vagovszky/iot/images/board/board_bottom.png

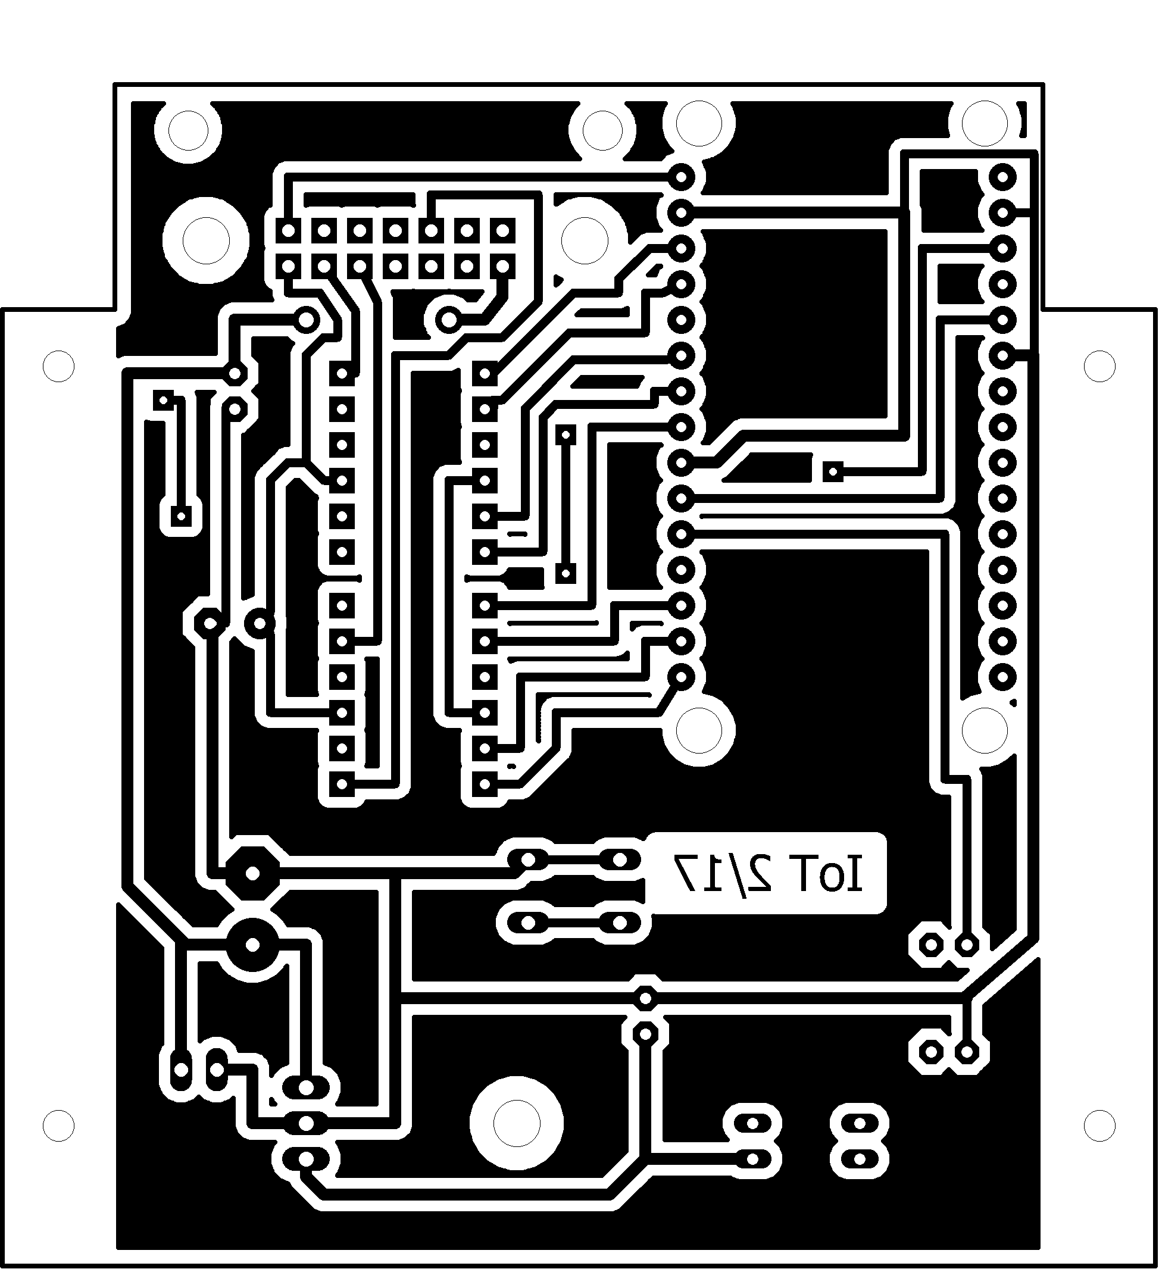
images/board/board_bottom.png
