vagovszky/iot/images/board/board_top.png

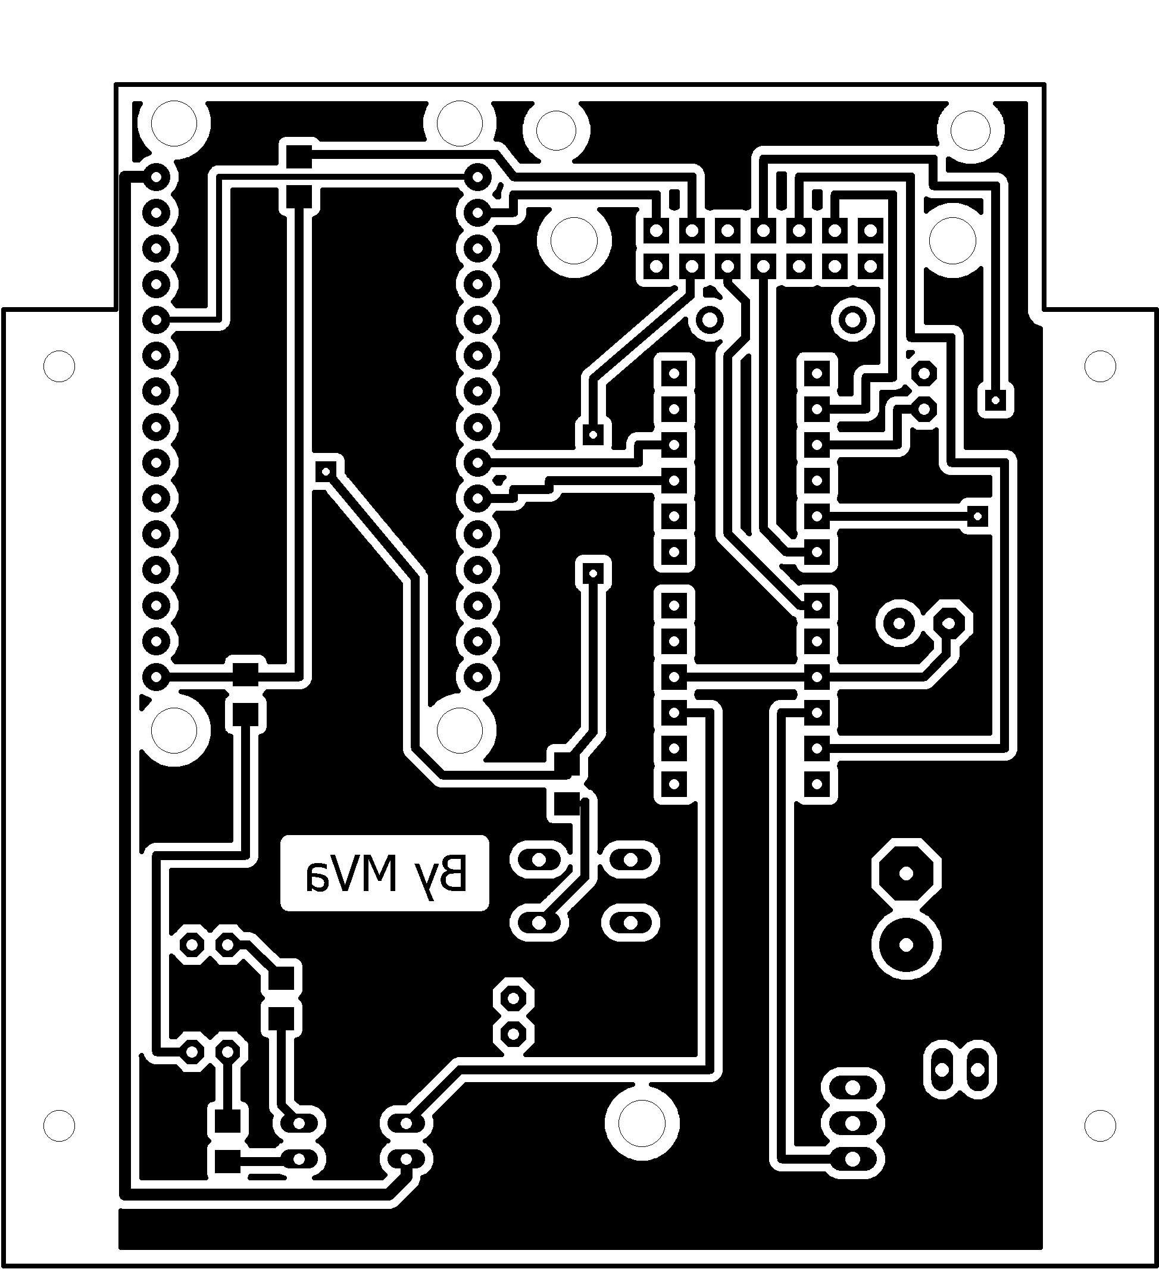
images/board/board_top.png
