vagovszky/iot/images/board/mod_io_board_bottom.png

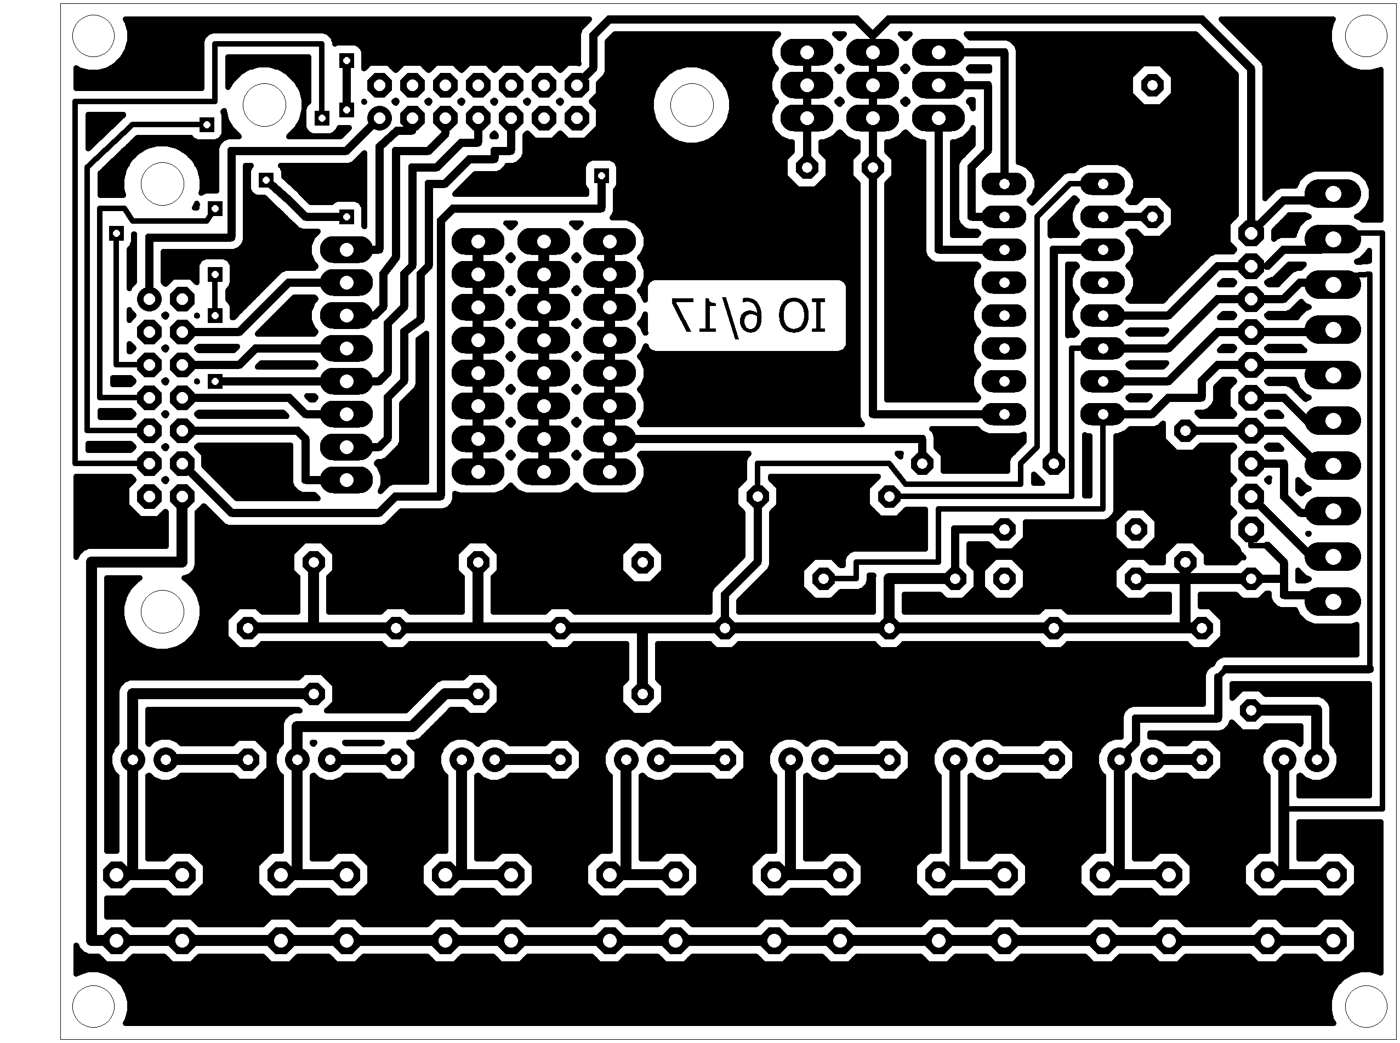
images/board/mod_io_board_bottom.png
