vagovszky/iot/images/board/mod_io_board_bottom_mask.png

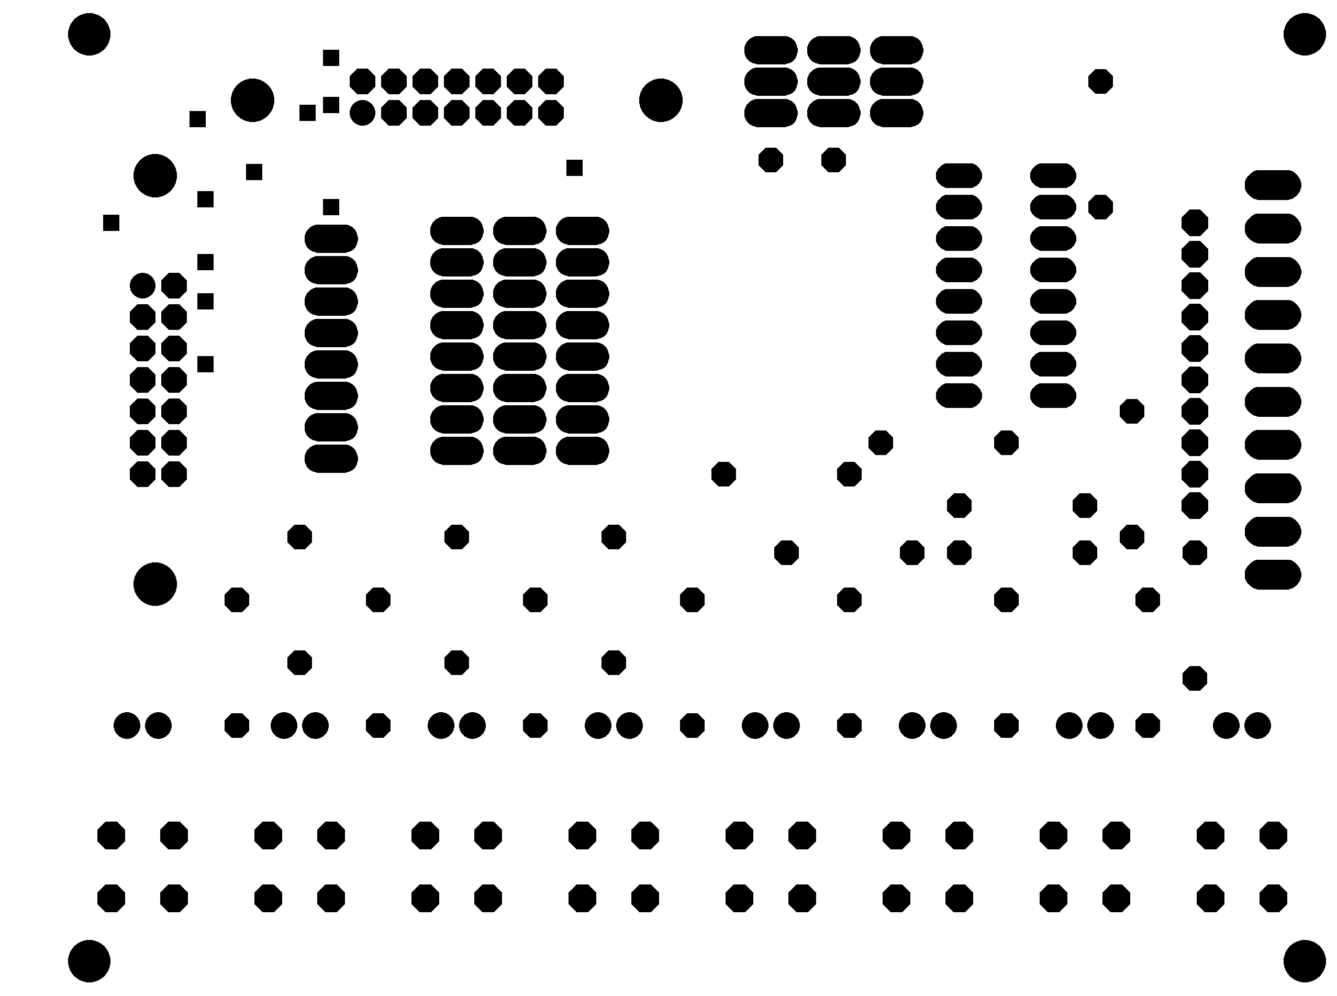
images/board/mod_io_board_bottom_mask.png
