vagovszky/iot/images/board/mod_io_board_top.png

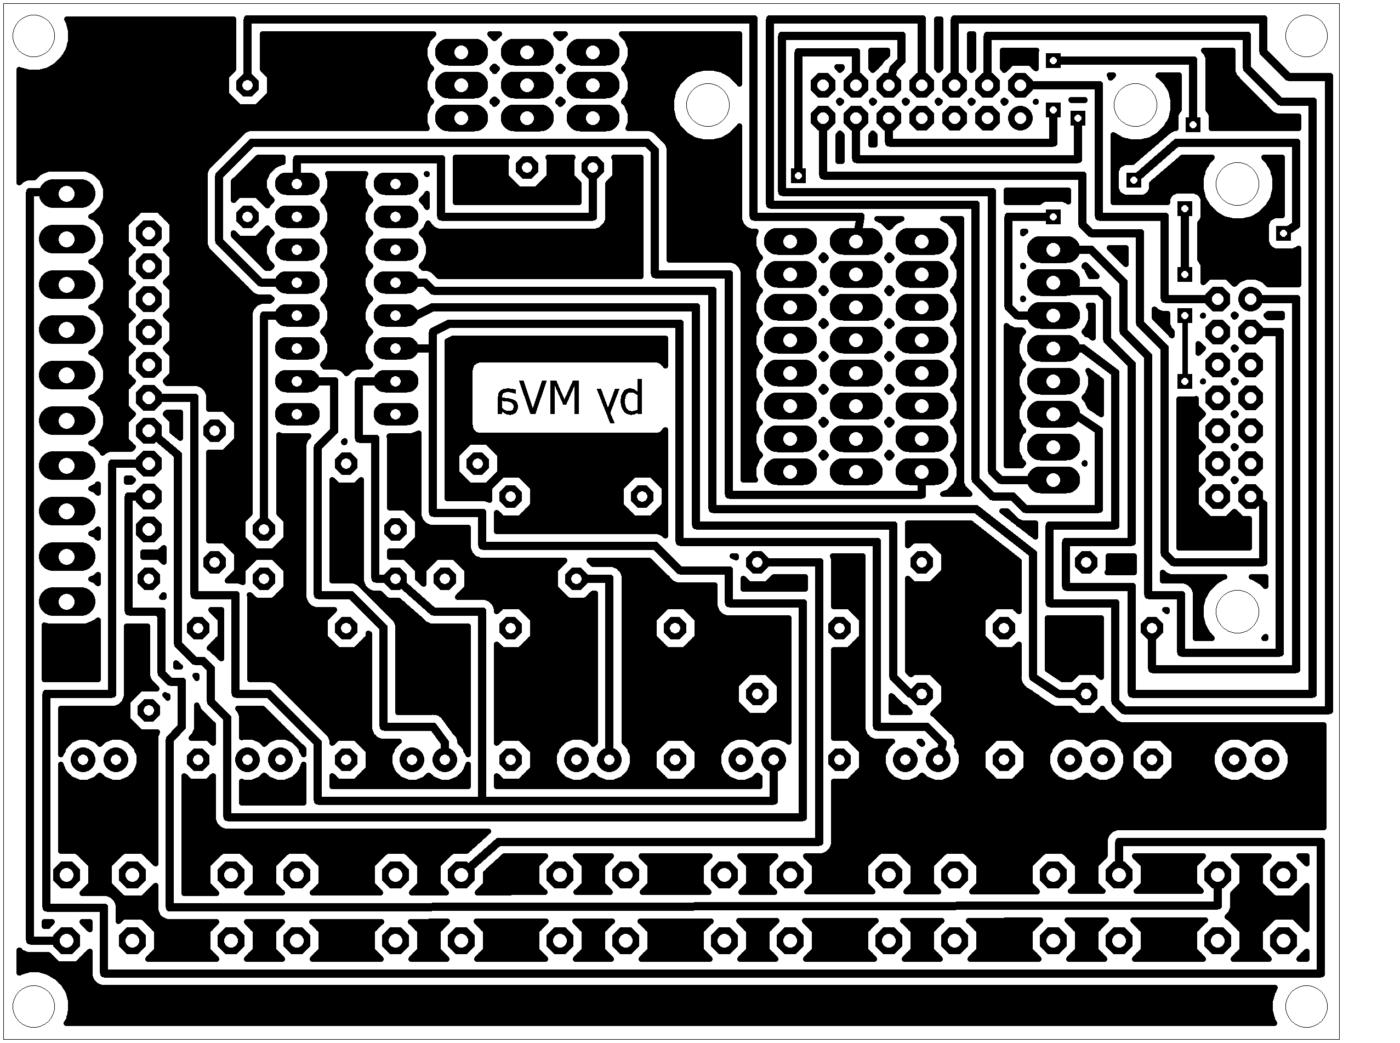
images/board/mod_io_board_top.png
