vagovszky/iot/images/board/mod_io_board_top_mask.png

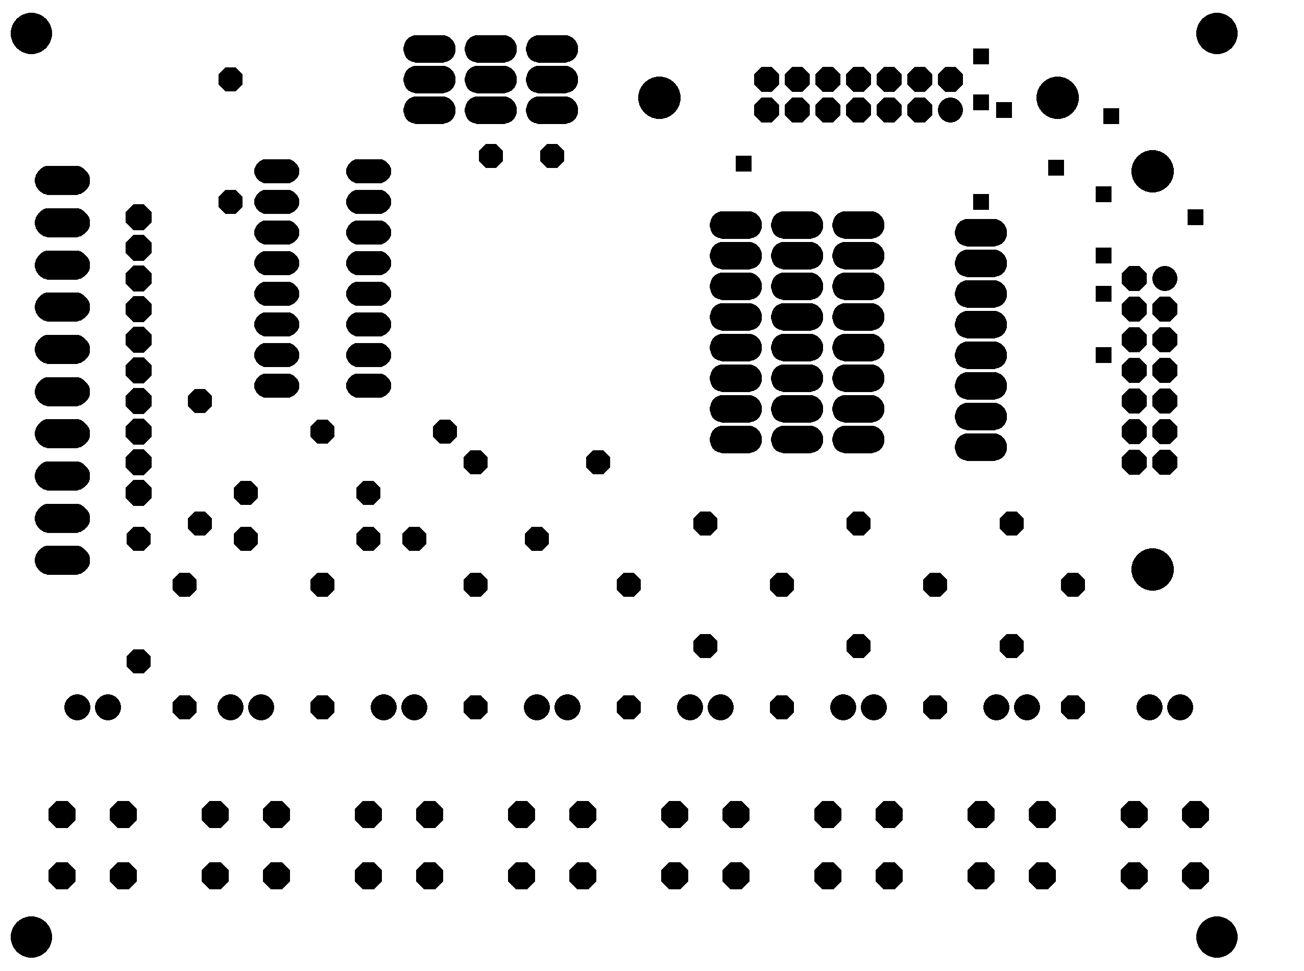
images/board/mod_io_board_top_mask.png
