vagovszky/iot/images/board/mod_temp_board_600dpi.png

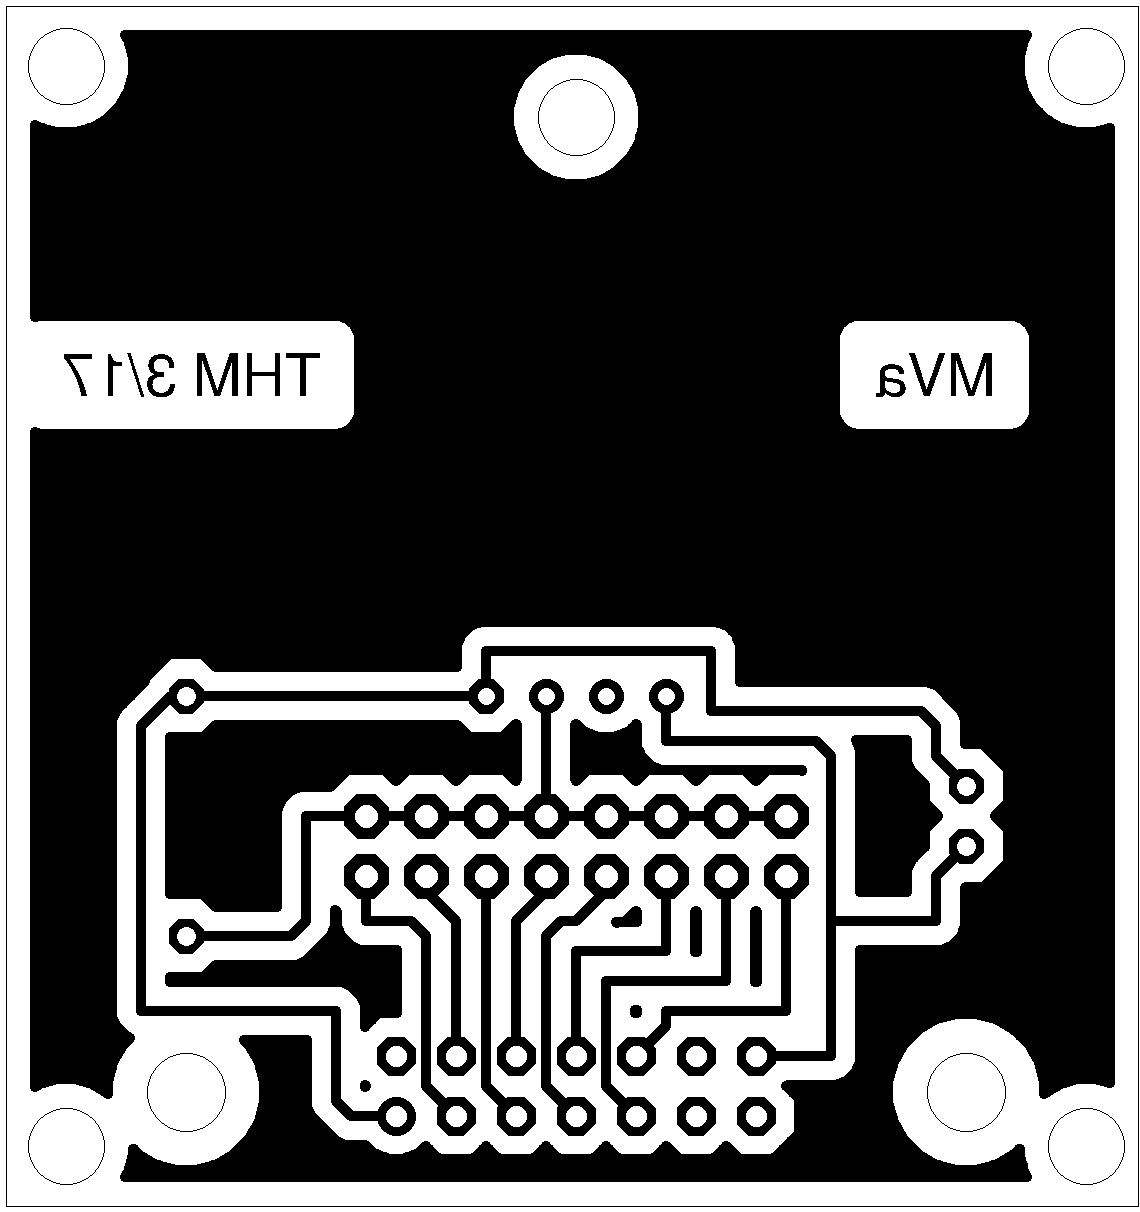
images/board/mod_temp_board_600dpi.png
