vagovszky/iot/images/board/mod_temp_mask_600dpi.png

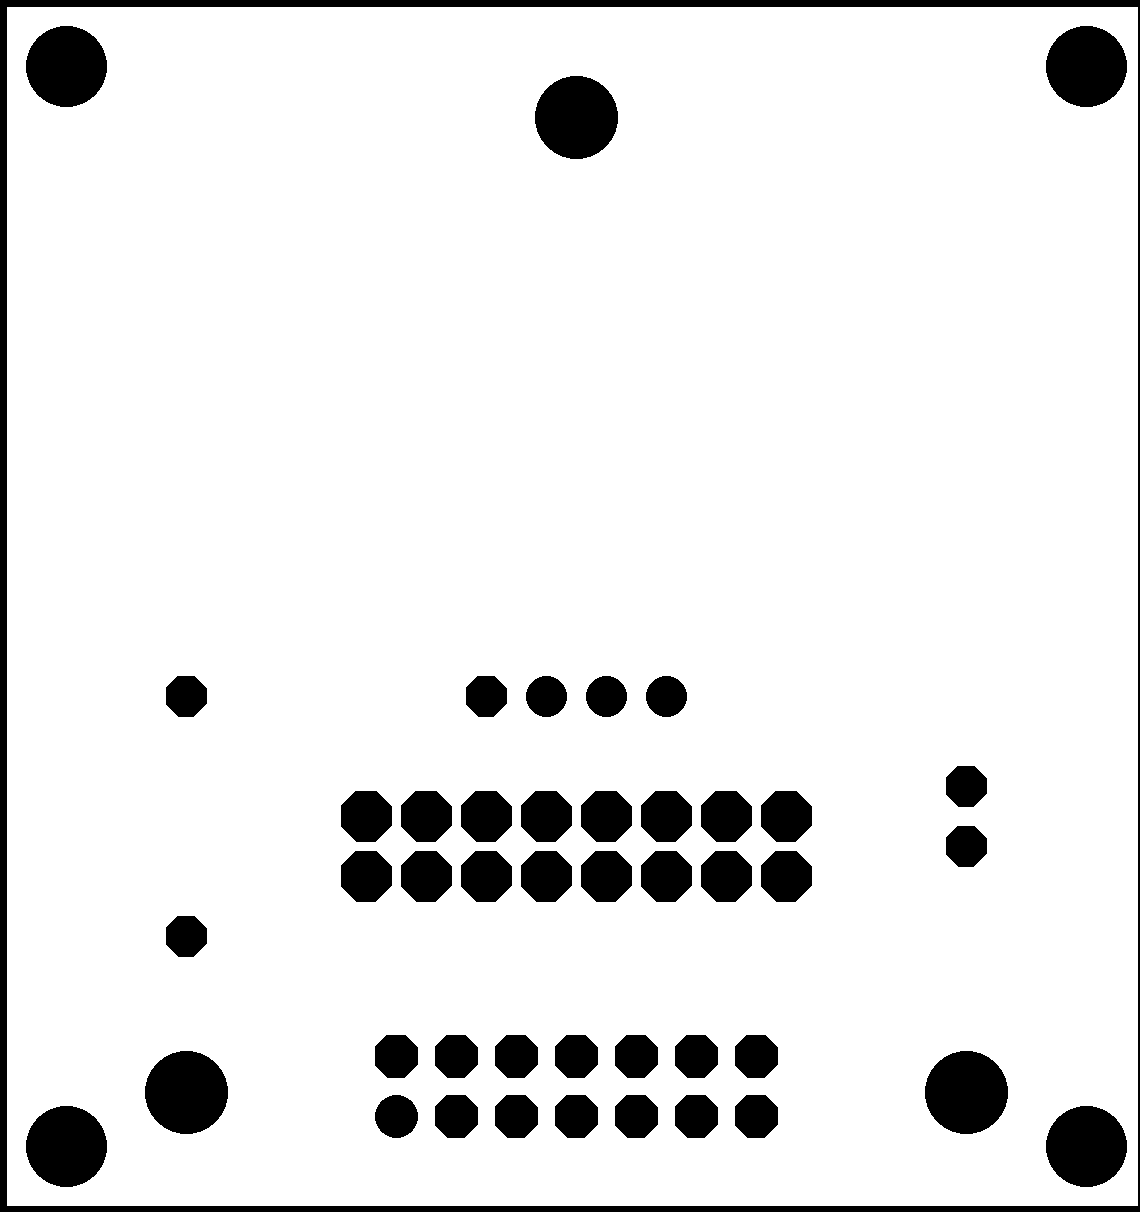
images/board/mod_temp_mask_600dpi.png
