vagovszky/iot/images/board/osaz.png

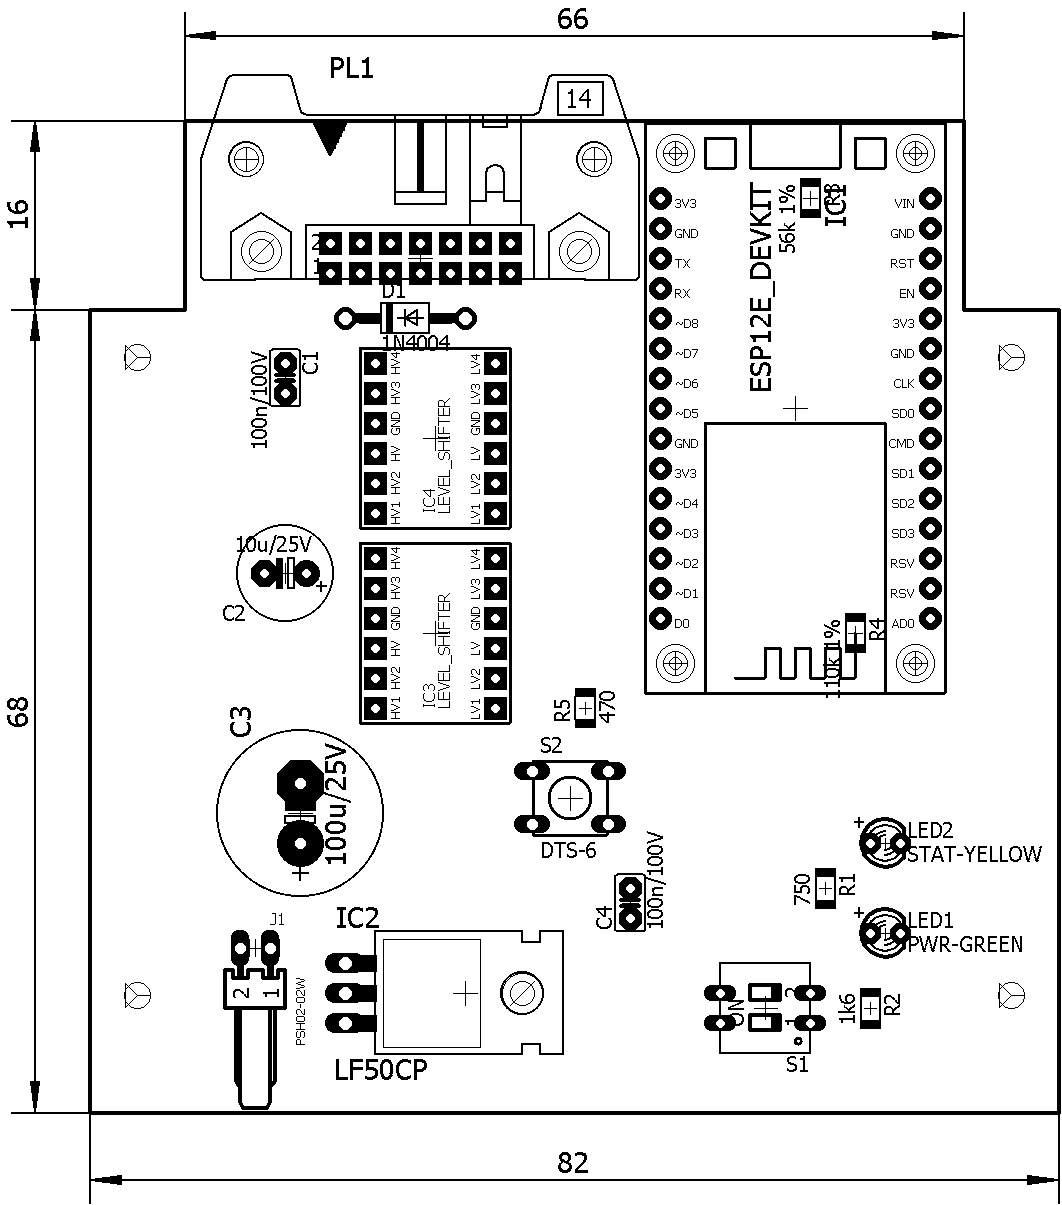
images/board/osaz.png
