vagovszky/iot/images/fotky/deska-osazena.jpg

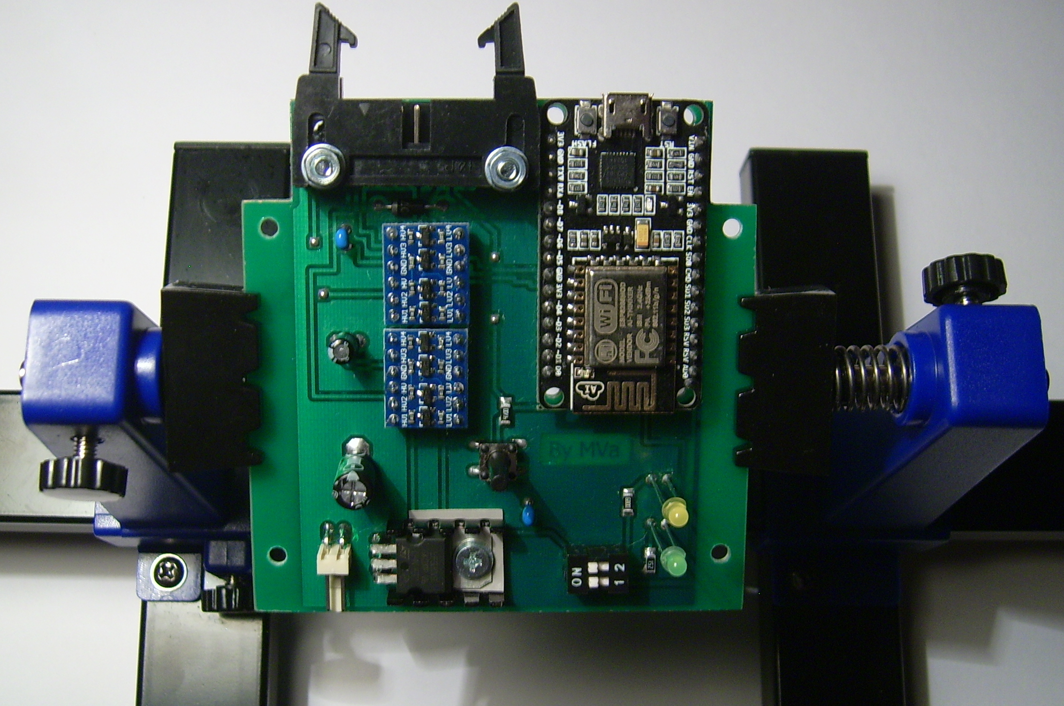
images/fotky/deska-osazena.jpg
