vagovszky/iot/images/fotky/deska-pred-vrtanim.jpg

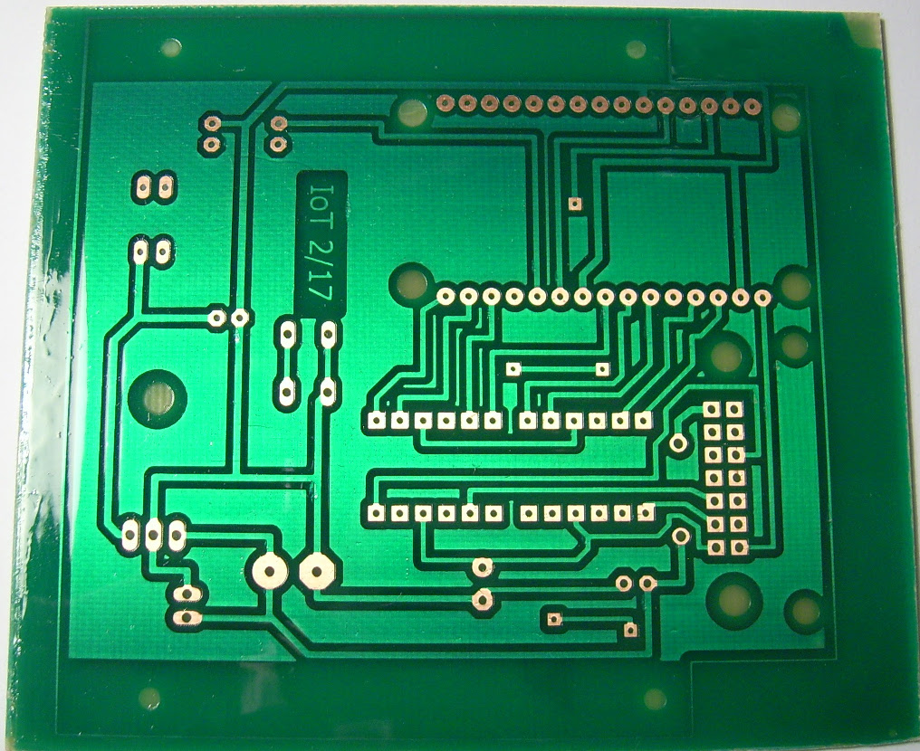
images/fotky/deska-pred-vrtanim.jpg
