vagovszky/iot/images/fotky/modul-hlavni.jpg

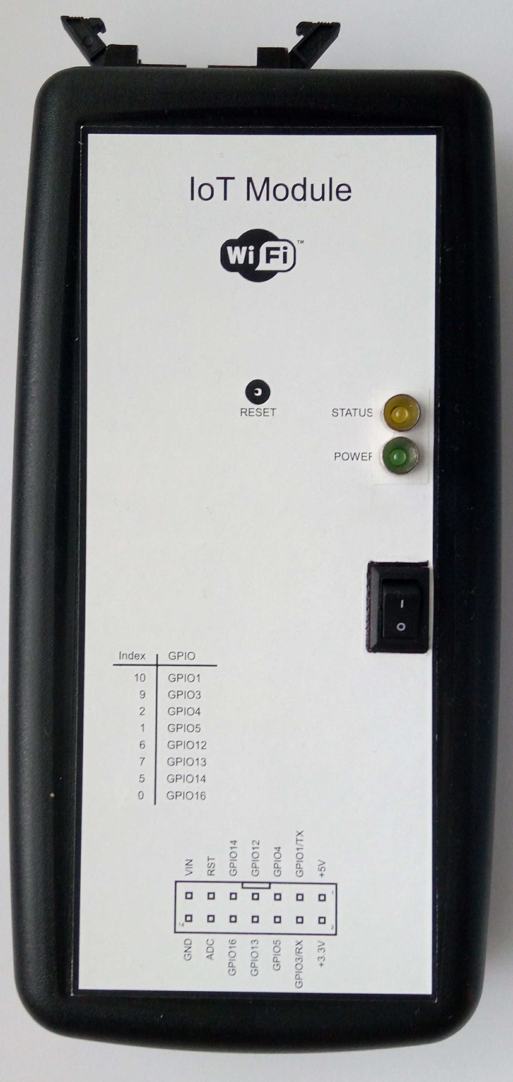
images/fotky/modul-hlavni.jpg
