vagovszky/iot/images/fotky/modul-io.jpg

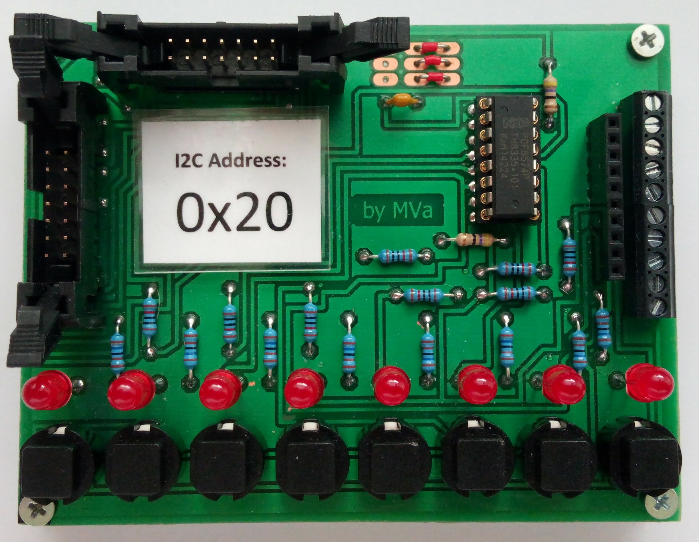
images/fotky/modul-io.jpg
