vagovszky/iot/images/fotky/modul-otevreny.jpg

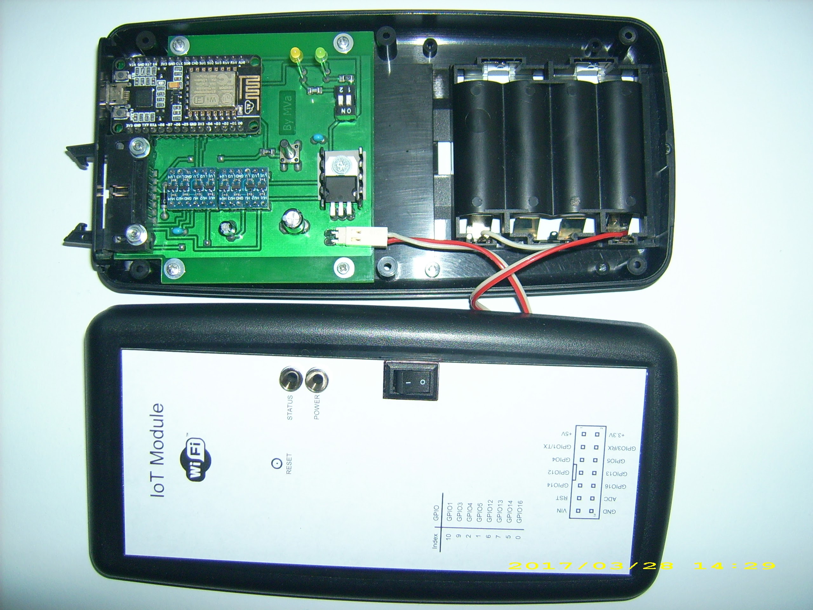
images/fotky/modul-otevreny.jpg
