vagovszky/iot/images/fotky/modul-teplota-vlhkost.jpg

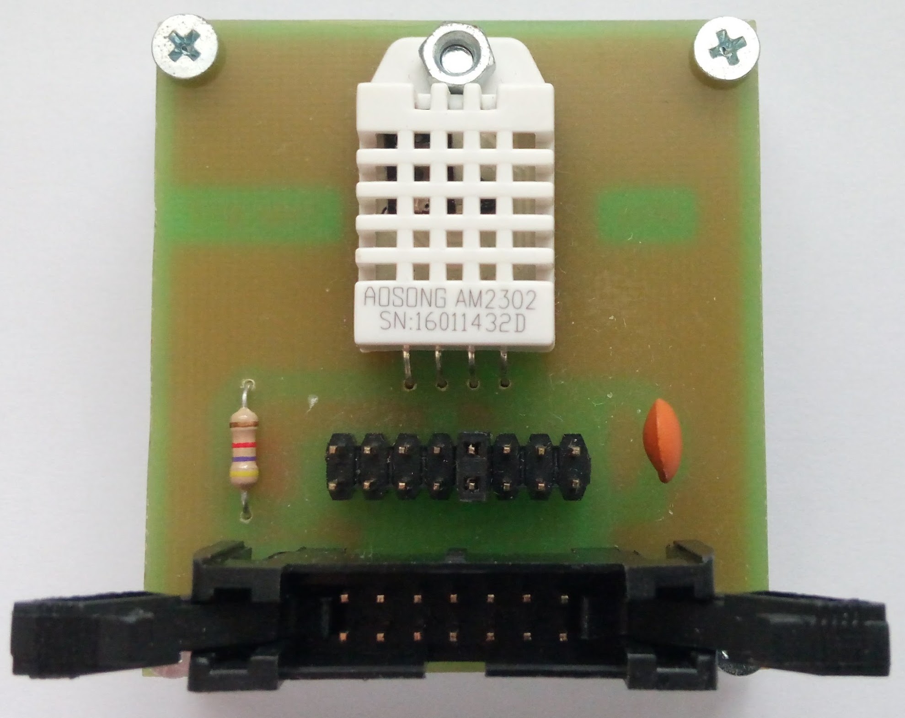
images/fotky/modul-teplota-vlhkost.jpg
