vagovszky/iot/images/fotky/modul-zadni-strana.jpg

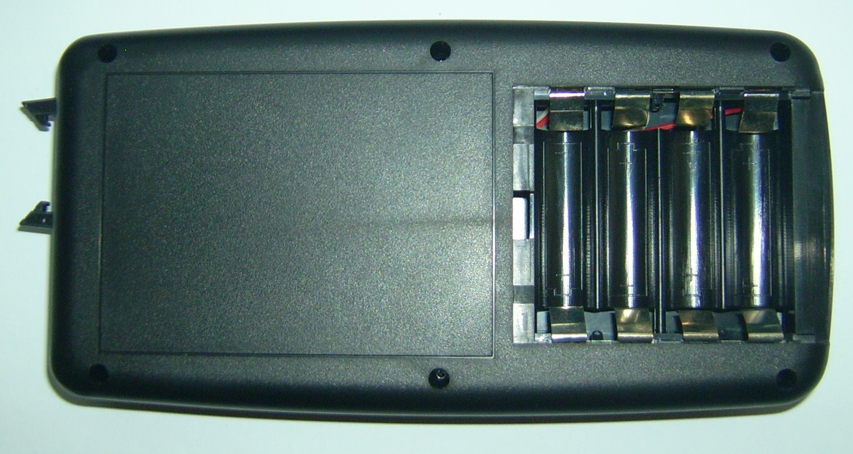
images/fotky/modul-zadni-strana.jpg
