vagovszky/iot/images/fotky/modul.jpg

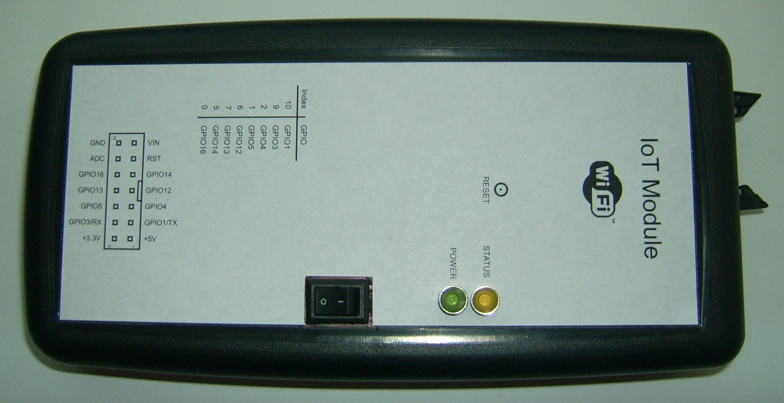
images/fotky/modul.jpg
