vagovszky/iot/images/fotky/napajeci-adapter.jpg

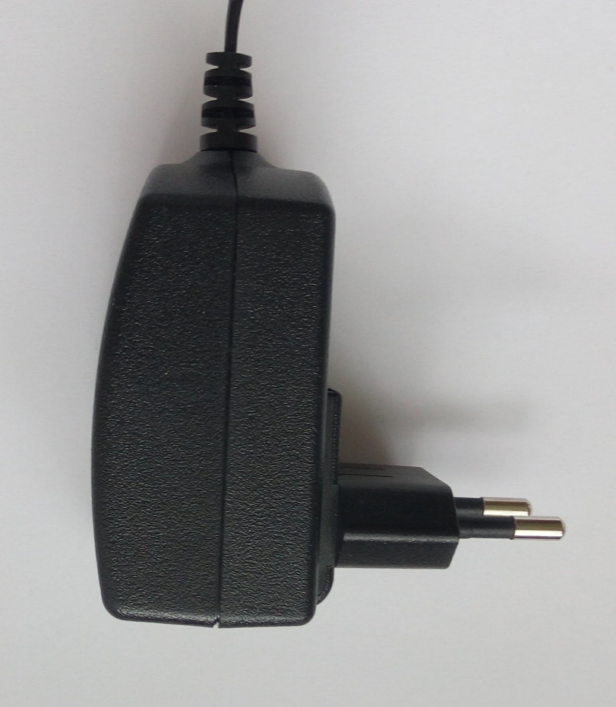
images/fotky/napajeci-adapter.jpg
