vagovszky/iot/images/fotky/panel-predni.jpg

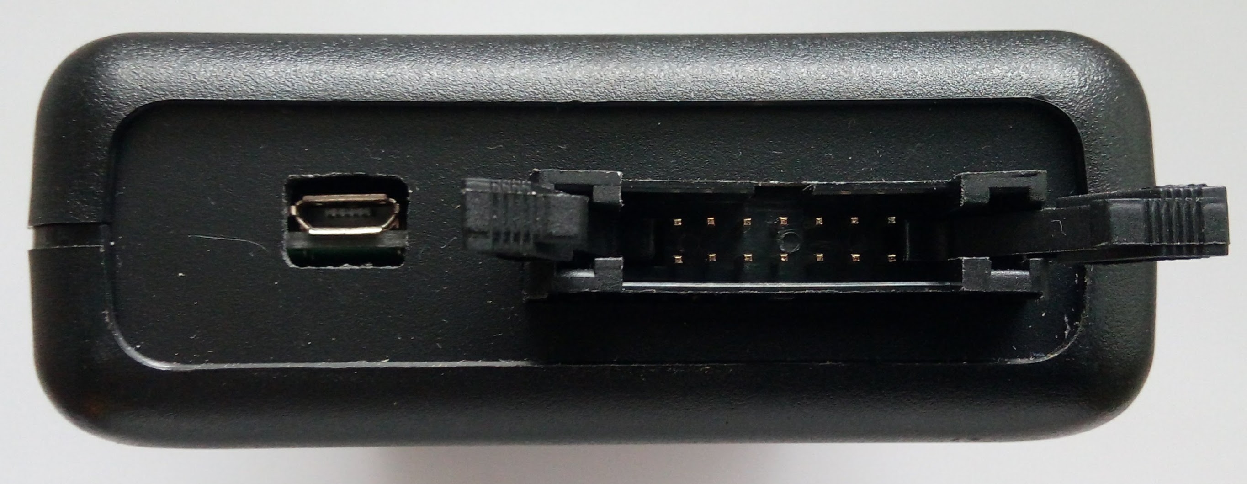
images/fotky/panel-predni.jpg
