vagovszky/iot/images/fotky/raspbery2.jpg

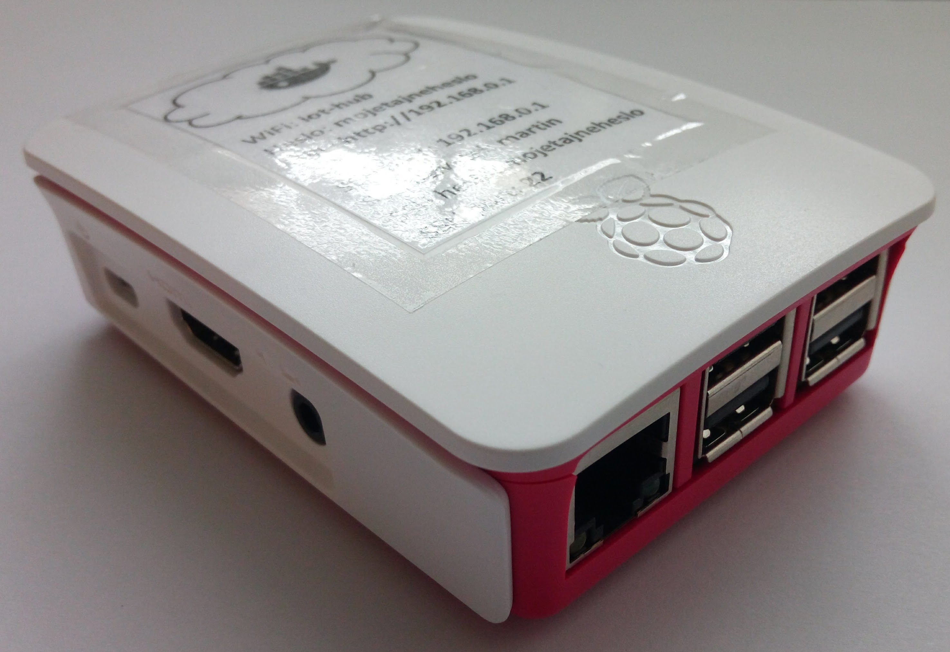
images/fotky/raspbery2.jpg
