vagovszky/iot/images/fotky/raspbery-bocni.jpg

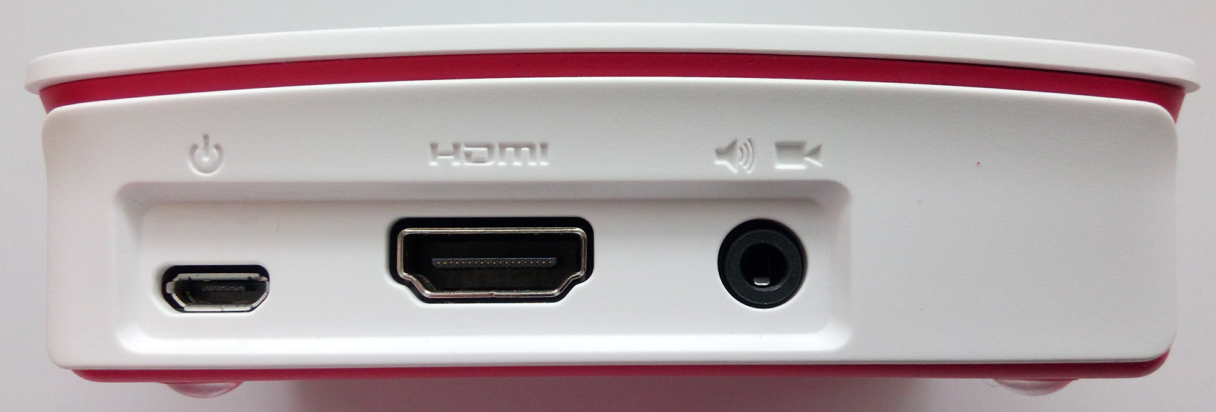
images/fotky/raspbery-bocni.jpg
