vagovszky/iot/images/fotky/raspbery-predni.jpg

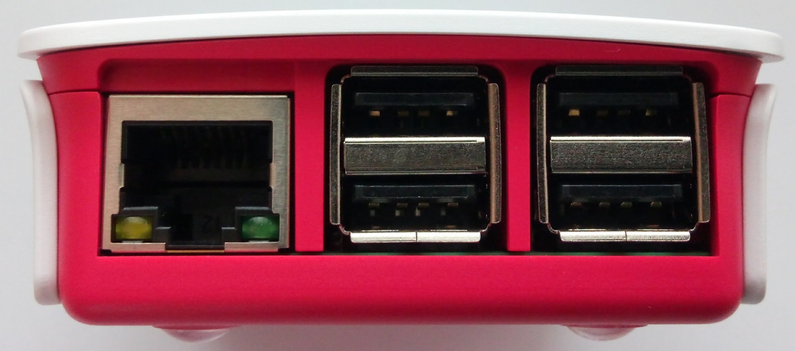
images/fotky/raspbery-predni.jpg
