vagovszky/iot/images/fotky/raspbery.jpg

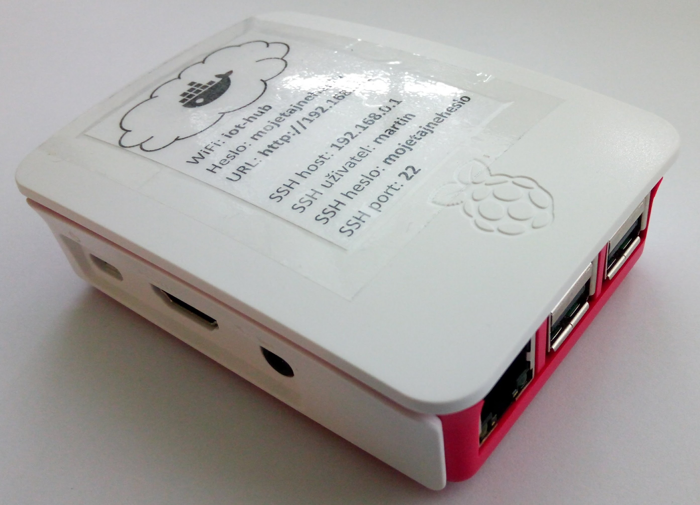
images/fotky/raspbery.jpg
