vagovszky/iot/images/hardware/board_white_bg.png

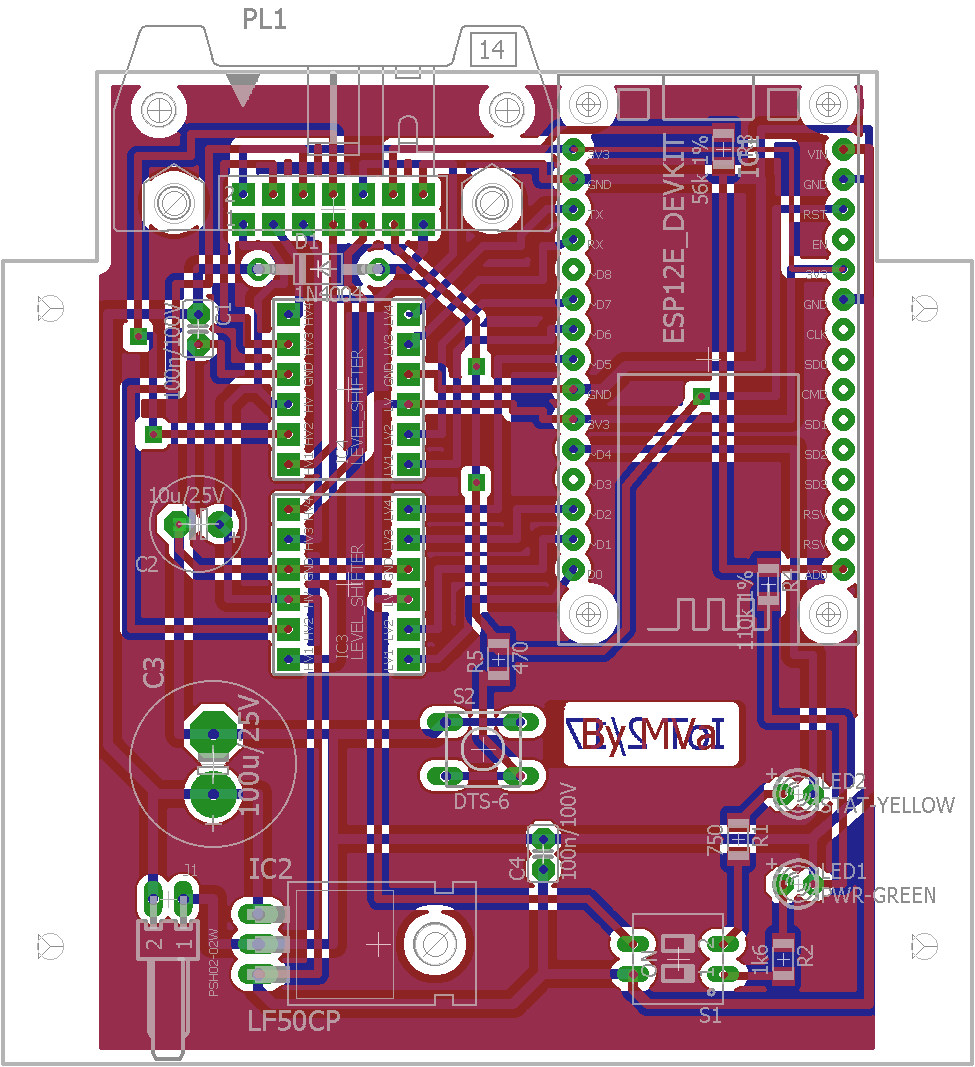
images/hardware/board_white_bg.png
