vagovszky/iot/images/hardware/mod_io_board.png

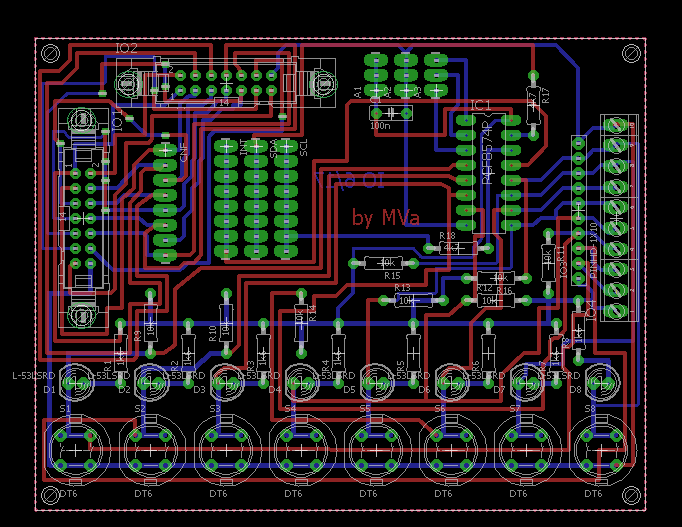
images/hardware/mod_io_board.png
