vagovszky/iot/images/hardware/mod_io_schema.png

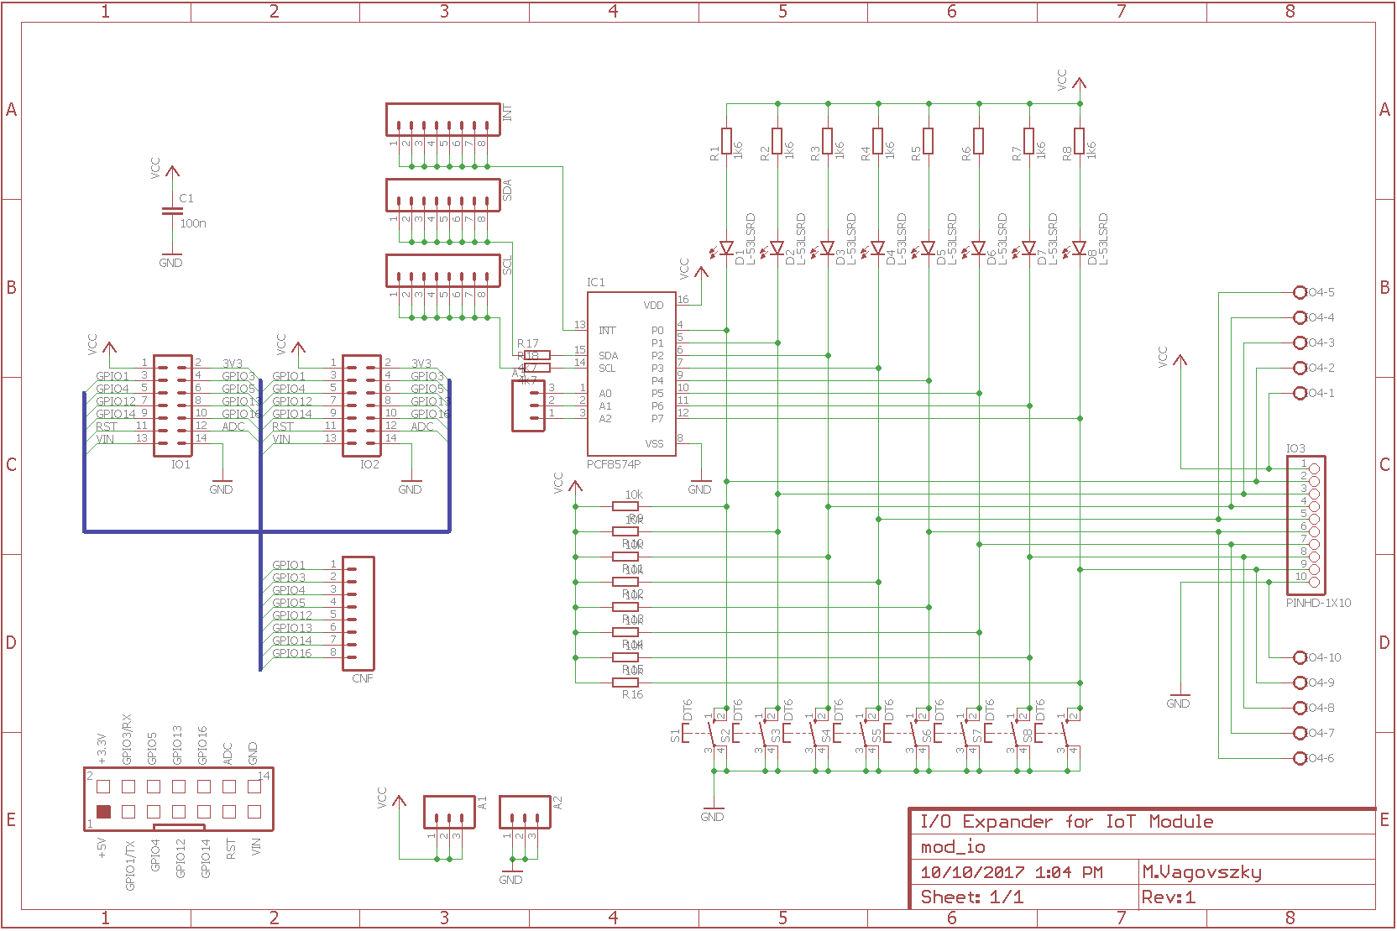
images/hardware/mod_io_schema.png
