vagovszky/iot/images/hardware/mod_temperature_board_white.png

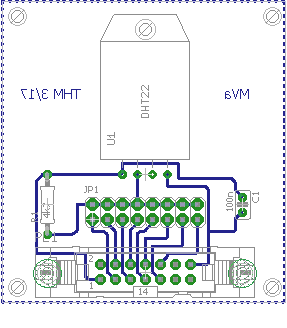
images/hardware/mod_temperature_board_white.png
