vagovszky/iot/images/hardware/mod_temperature_osaz.png

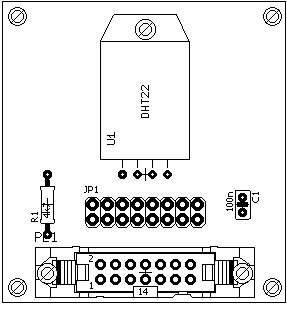
images/hardware/mod_temperature_osaz.png
