vagovszky/iot/images/hardware/schema.png

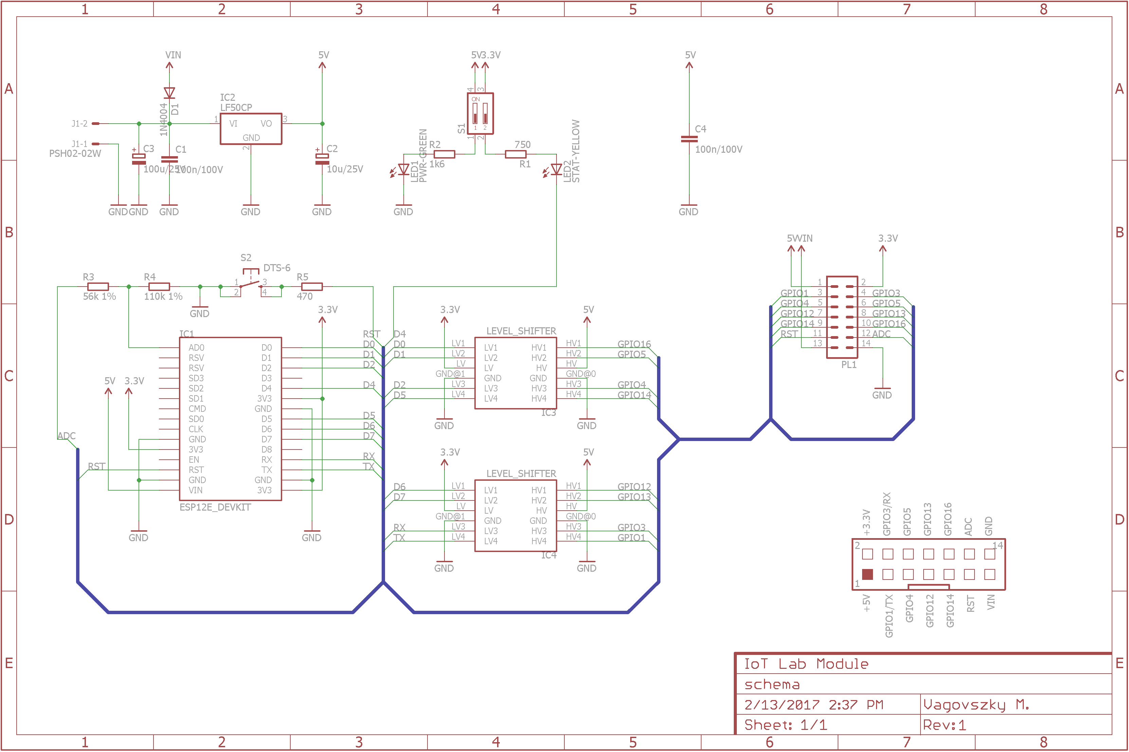
images/hardware/schema.png
