vagovszky/iot/images/board/board_bottom_soldermask.png

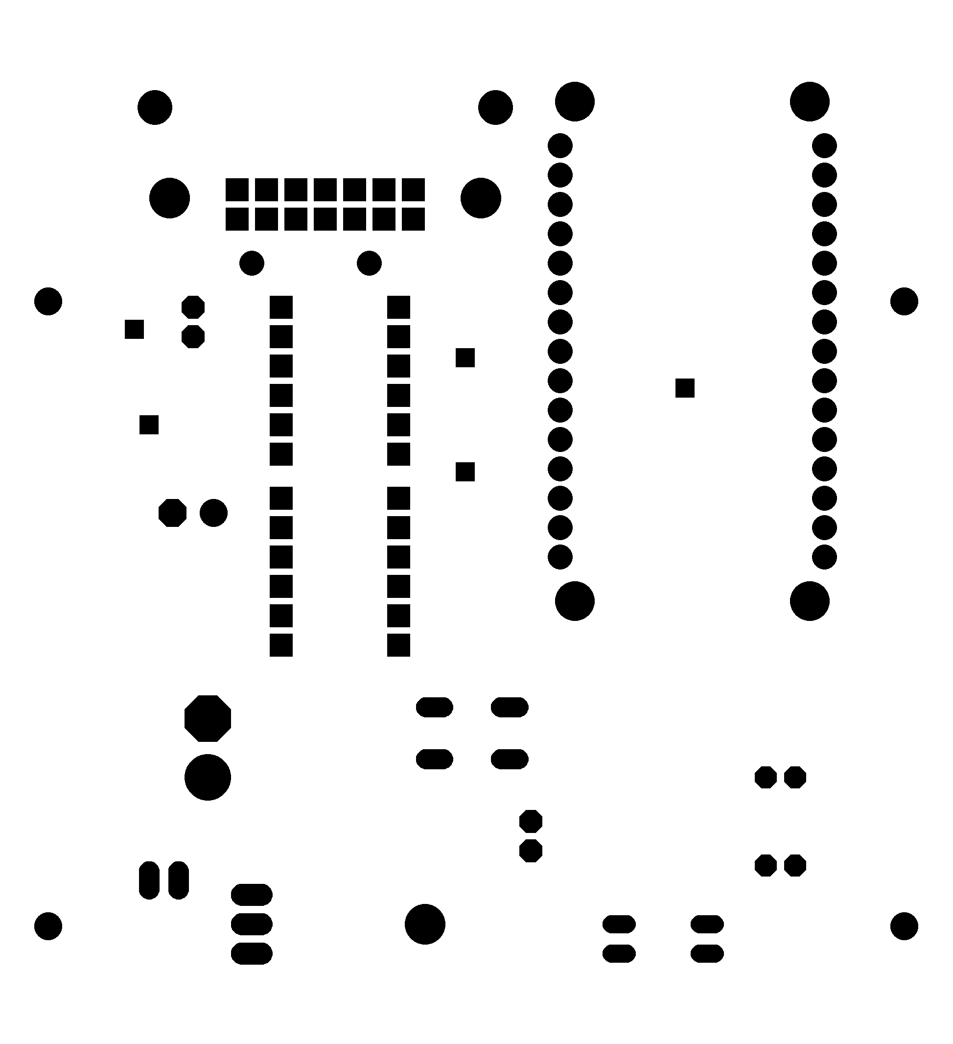
images/board/board_bottom_soldermask.png
