vagovszky/iot/images/board/board_top_soldermask.png

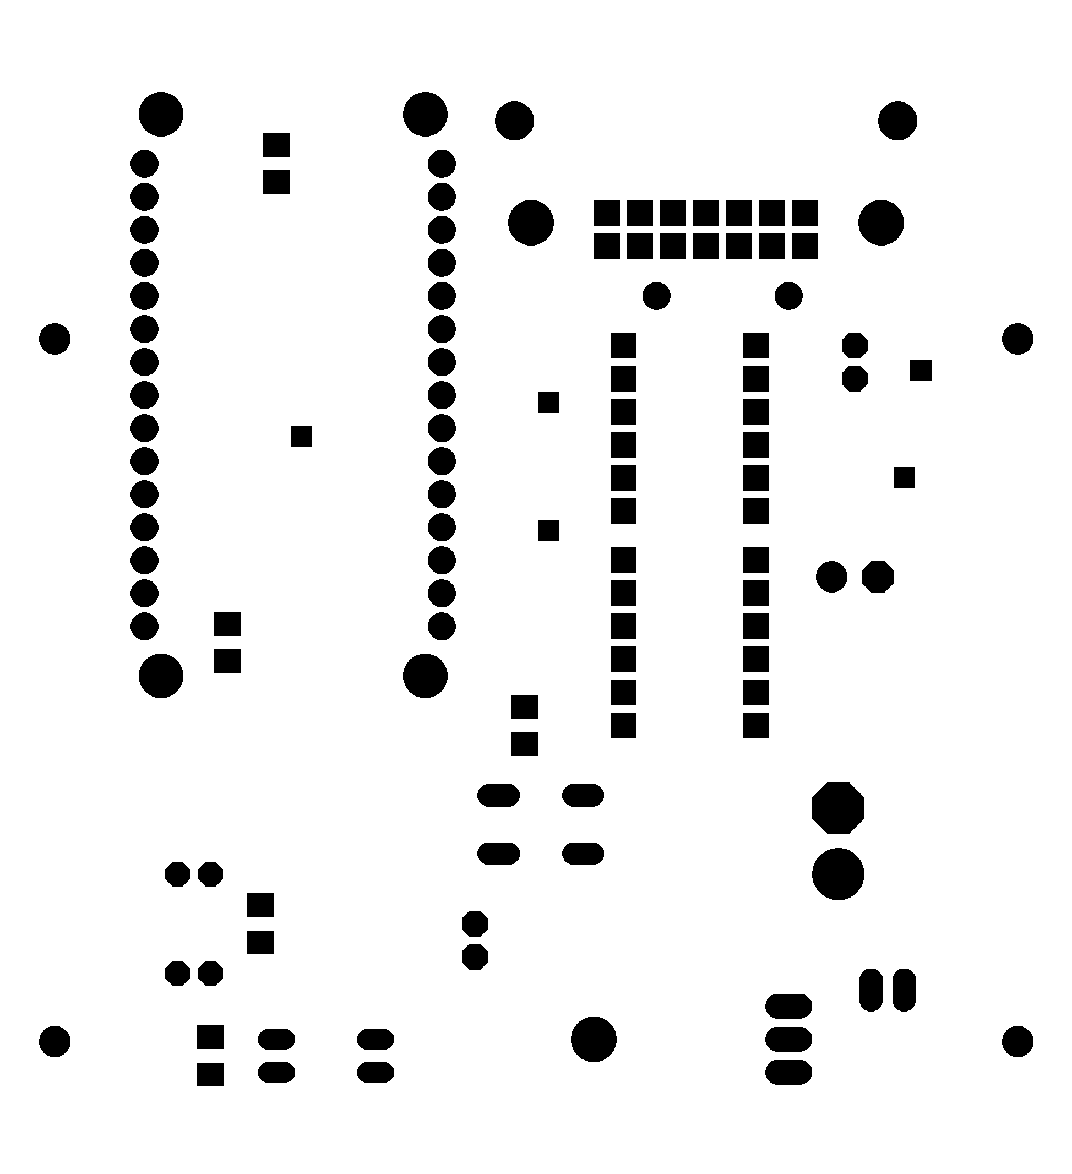
images/board/board_top_soldermask.png
